f-w-robots/RBT/ultrasonic/EngineStep.h

//#ifndef EnigneStep_h
//#define EngineStep_h
//
//#include "Motor28BYJ.h"
//
//class EngineStep
//{
//  public:
//    EngineStep(Motor28BYJ* motor);
//    void command(String command);
//  private:
//    void forward();
//    void revert();
//    void left();
//    void right();
//    Motor28BYJ* _motor;
//    const int defaultSpeed = 150;
//};
//
//#endif
