f-w-robots/RBT/ultrasonic/ESP8266Serial.cpp

#include "Arduino.h"

#include "ESP8266Serial.h"

ESP8266Serial::ESP8266Serial() {
  _buff[0] = 0;
  _connection_timeout = 0;
  _espReady = false;
  _wifi = false;
  _socket = false;
  _string = "";
}

int ESP8266Serial::status() {
  if (!_espReady)
    return 0;
  if (!_wifi)
    return 2;
  if (!_socket)
    return 4;
  return 8;
}

void ESP8266Serial::request(String string) {
  if (_socket) {
    Serial.println(string);
  }
}

boolean ESP8266Serial::prepare() {
  Serial.println("AT:reset");
  _espReady = responseIsOK("reset");
  return _espReady;
}

boolean ESP8266Serial::upWiFi(String ssid, String password) {
  if (!_espReady) {
    return false;
  }
  Serial.println("AT:setup+" + ssid + "+" + password);
  _wifi = responseIsOK("wifi");
  return _wifi;
}

boolean ESP8266Serial::connectToSocket(String host, String port, String sha) {
  if (!_wifi) {
    return false;
  }
  Serial.println("AT:connect+" + host + "+" + port + "+/" + sha);
  _socket = responseIsOK("connect");
  return _socket;
}

boolean ESP8266Serial::responseIsOK(String type) {
  String resp = response();
  return resp.endsWith("OK:" + type);
}

boolean ESP8266Serial::responseAvailable() {
  return Serial.available() > 0;
}

String ESP8266Serial::getResponse() {
  if (!_socket)
    return "FAIL: not socket";
  while (Serial.available() > 0) {
    if (readString(Serial.read())) {
      _string = getBuffString();
      if (_string.startsWith("FAIL:"))
        _socket = false;

      return _string;
    }
  }
  return "";
}

boolean ESP8266Serial::connected() {
  return _socket;
}

String ESP8266Serial::response() {
  while (true) {
    while (Serial.available() > 0) {
      char b = Serial.read();
      if (readString(b)) {
        _string = getBuffString();

        return _string;
      }
    }
  }
}

boolean ESP8266Serial::readString(char b) {
  int len = strlen(_buff);

  if (len >= 255) {
    _buff[255] = 0;
    return true;
  }

  if (b == 0x0A) {
    if (len > 0 && _buff[len - 1] == 0x0D) {
      _buff[len - 1] = 0;
      return true;
    }
  } else {
    _buff[len] = b;
    _buff[len + 1] = 0;
    return false;
  }
}

String ESP8266Serial::getBuffString() {
  _string = String(_buff);
  _buff[0] = 0;
  return _string;
}
